hmaerki/experiment_octoprobe_testbed_heatguard/kicad/heatguard_v0.3/production_v0.3/pcb_top_3D.png

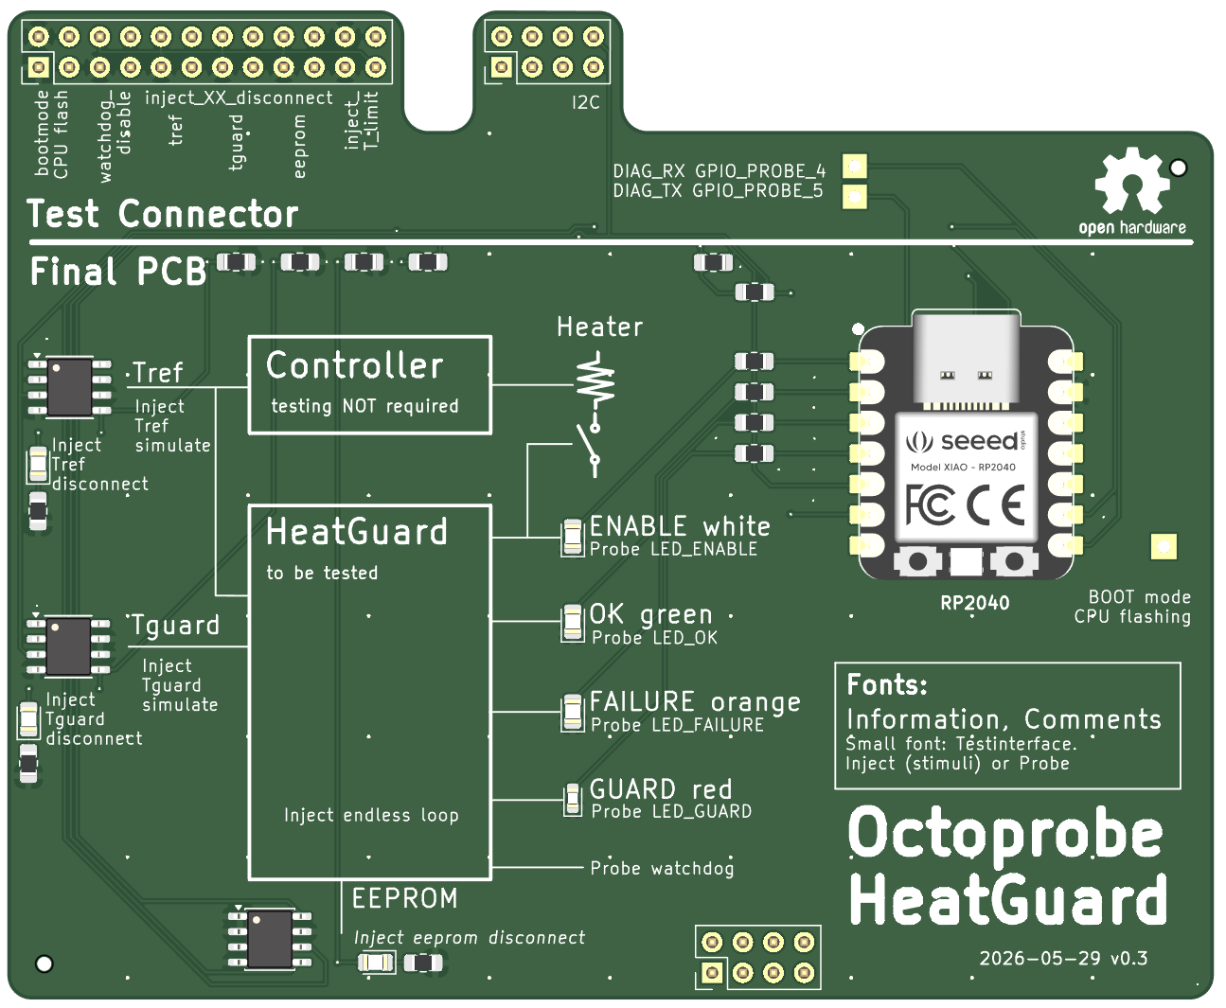
kicad/heatguard_v0.3/production_v0.3/pcb_top_3D.png
