hmaerki/experiment_octoprobe_testbed_heatguard/experiments/micropython_ds20_simulator/main.py

"""
DS18B20 1-Wire Slave Implementation for Raspberry Pi Pico

This file contains MicroPython code running on a Raspberry Pi Pico.

GPIO Configuration:
- GPIO2: Connected to a 1-Wire bus (open-drain with 4.7k pull-up)

This Pico acts as a 1-WIRE SLAVE and emulates two DS18B20 temperature sensors:
- Sensor 1: ROM 28 5A 3F 7B 05 00 00 0F → 18°C
- Sensor 2: ROM 28 5A 3F 7B 05 00 00 00 → 12°C

Reference: https://www.analog.com/media/en/technical-documentation/data-sheets/ds18b20.pdf

The implementation handles:
- 1-Wire reset and presence pulse detection
- ROM identification and matching (SEARCH_ROM, MATCH_ROM, SKIP_ROM)
- Temperature conversion requests
- Scratchpad memory read/write operations
"""

import time

import machine
from micropython import const

# ============================================================================
# GPIO Configuration
# ============================================================================

ONEWIRE_PIN = 2  # GPIO2 - 1-Wire data line
onewire_pin = machine.Pin(ONEWIRE_PIN, machine.Pin.OPEN_DRAIN, machine.Pin.PULL_UP)

# ============================================================================
# 1-Wire Timing Constants (microseconds)
# ============================================================================

RESET_LOW_TIME = const(480)  # Master reset pulse duration
PRESENCE_DELAY = const(30)  # Delay before responding with presence
PRESENCE_PULSE_TIME = const(60)  # Our presence pulse duration
READ_SAMPLE_TIME = const(15)  # Time to read bit during read slot
WRITE_0_TIME = const(60)  # Hold time for writing 0
WRITE_1_TIME = const(15)  # Hold time for writing 1
BIT_SLOT_TIME = const(60)  # Total time per bit slot

# ============================================================================
# 1-Wire Command Codes
# ============================================================================

CMD_SEARCH_ROM = const(0xF0)
CMD_READ_ROM = const(0x33)
CMD_MATCH_ROM = const(0x55)
CMD_SKIP_ROM = const(0xCC)
CMD_ALARM_SEARCH = const(0xEC)
CMD_CONVERT_TEMP = const(0x44)
CMD_WRITE_SCRATCHPAD = const(0x4E)
CMD_READ_SCRATCHPAD = const(0xBE)
CMD_COPY_SCRATCHPAD = const(0x48)
CMD_RECALL_E2 = const(0xB8)
CMD_READ_POWER_SUPPLY = const(0xB4)

# ============================================================================
# Sensor Configuration
# ============================================================================

FAMILY_CODE = const(0x28)  # DS18B20 family code

# Define two virtual sensors with their ROM codes and temperatures
SENSORS = [
    {
        "rom": bytes([0x28, 0x5A, 0x3F, 0x7B, 0x05, 0x00, 0x00, 0x0F]),
        "temp": 18.0,
        "name": "Sensor 1",
    },
    {
        "rom": bytes([0x28, 0x5A, 0x3F, 0x7B, 0x05, 0x00, 0x00, 0x00]),
        "temp": 12.0,
        "name": "Sensor 2",
    },
]

# ============================================================================
# CRC-8 Calculation
# ============================================================================


def crc8(data):
    """Calculate CRC-8 for 1-Wire (polynomial 0x31)"""
    crc = 0
    for byte in data:
        crc ^= byte
        for _ in range(8):
            if crc & 0x01:
                crc = (crc >> 1) ^ 0x8C
            else:
                crc >>= 1
    return crc & 0xFF


# ============================================================================
# Scratchpad Memory Class
# ============================================================================


class Scratchpad:
    """DS18B20 Scratchpad memory (9 bytes)"""

    def __init__(self, temp=20.0):
        self.set_temperature(temp)
        self.th = 0x4B  # Byte 2: TH (75°C)
        self.tl = 0x46  # Byte 3: TL (70°C)
        self.config = 0x7F  # Byte 4: CONFIG (12-bit resolution)

    def set_temperature(self, celsius):
        """Set temperature in Celsius and encode to LSB/MSB"""
        # Clamp temperature to valid range
        celsius = max(-55.0, min(125.0, celsius))

        # Convert to 1/16°C units
        temp_int = int(celsius * 16)

        # Encode as 16-bit signed
        if temp_int < 0:
            temp_int = (((-temp_int) ^ 0xFFFF) + 1) & 0xFFFF

        self.temp_lsb = temp_int & 0xFF
        self.temp_msb = (temp_int >> 8) & 0xFF

    def to_bytes(self):
        """Convert scratchpad to 9-byte array"""
        data = bytes(
            [
                self.temp_lsb,
                self.temp_msb,
                self.th,
                self.tl,
                self.config,
                0xFF,  # Reserved
                0x00,  # Reserved
                0x00,  # Reserved
                0x00,  # CRC (will be filled)
            ]
        )

        # Calculate CRC for bytes 0-7
        crc = crc8(data[0:8])
        data = data[0:8] + bytes([crc])

        return data


# ============================================================================
# 1-Wire Slave Implementation
# ============================================================================


class OneWireSlave:
    """1-Wire Slave implementation for DS18B20 emulation"""

    def __init__(self, pin, sensors):
        self.pin = pin
        self.sensors = sensors
        self.selected_sensor = None
        self.rom_bit_index = 0
        self.conversion_active = False

    def wait_for_reset(self):
        """Wait for a 1-Wire reset pulse from master"""
        # Wait for line to go low (reset pulse from master)
        timeout = 1000  # 1 second timeout
        count = 0

        while self.pin.value() and count < timeout:
            time.sleep_us(100)
            count += 1

        if count >= timeout:
            return False

        # Wait for reset pulse to complete (480-960 us)
        time.sleep_us(RESET_LOW_TIME)

        # Check if line is still low (valid reset pulse)
        if not self.pin.value():
            return False

        # Send presence pulse
        self.send_presence_pulse()
        return True

    def send_presence_pulse(self):
        """Send presence pulse to indicate we're on the bus"""
        # Wait a bit before pulling line low
        time.sleep_us(PRESENCE_DELAY)

        # Pull line low for presence pulse
        self.pin.value(0)
        time.sleep_us(PRESENCE_PULSE_TIME)

        # Release line
        self.pin.value(1)

    def read_bit(self):
        """Read a bit from the 1-Wire bus"""
        # Wait for master to pull line low
        timeout = 100
        count = 0
        while self.pin.value() and count < timeout:
            time.sleep_us(1)
            count += 1

        if count >= timeout:
            return None

        # Wait for proper read sample time
        time.sleep_us(READ_SAMPLE_TIME)

        # Sample the bit (1 = line is high, 0 = line is low)
        bit = self.pin.value()

        # Wait for rest of bit slot
        time.sleep_us(BIT_SLOT_TIME - READ_SAMPLE_TIME)

        return bit

    def write_bit(self, bit):
        """Write a bit to the 1-Wire bus"""
        if bit:
            # Write 1: let line float high (very brief pull-down or none)
            self.pin.value(1)
            time.sleep_us(WRITE_1_TIME)
        else:
            # Write 0: pull line low
            self.pin.value(0)
            time.sleep_us(WRITE_0_TIME)
            self.pin.value(1)

        # Wait for rest of bit slot
        time.sleep_us(BIT_SLOT_TIME - (WRITE_1_TIME if bit else WRITE_0_TIME))

    def read_byte(self):
        """Read a byte from the 1-Wire bus (LSB first)"""
        byte = 0
        for i in range(8):
            bit = self.read_bit()
            if bit is None:
                return None
            if bit:
                byte |= 1 << i
        return byte

    def write_byte(self, byte):
        """Write a byte to the 1-Wire bus (LSB first)"""
        for i in range(8):
            bit = (byte >> i) & 1
            self.write_bit(bit)

    def handle_search_rom(self):
        """Handle ROM SEARCH command"""
        # Send ROM bits with collision detection
        # For simplicity in slave mode, we'll handle single device addressing
        pass

    def handle_skip_rom(self):
        """Handle SKIP ROM command - select all devices"""
        self.selected_sensor = self.sensors[0] if len(self.sensors) == 1 else None

    def handle_match_rom(self):
        """Handle MATCH ROM command - select device by ROM code"""
        rom = bytes(self.read_byte() for _ in range(8))

        # Find matching sensor
        for sensor in self.sensors:
            if sensor["rom"] == rom:
                self.selected_sensor = sensor
                return True

        return False

    def handle_convert_temp(self):
        """Handle CONVERT TEMPERATURE command"""
        self.conversion_active = True
        # Simulate conversion delay (750ms for 12-bit)
        time.sleep_ms(750)
        self.conversion_active = False

    def handle_read_scratchpad(self):
        """Handle READ SCRATCHPAD command"""
        if not self.selected_sensor:
            return

        # Create scratchpad with current temperature
        scratchpad = Scratchpad(self.selected_sensor["temp"])
        data = scratchpad.to_bytes()

        # Send all 9 bytes
        for byte in data:
            self.write_byte(byte)

    def handle_write_scratchpad(self):
        """Handle WRITE SCRATCHPAD command"""
        if not self.selected_sensor:
            return

        # Read TH, TL, CONFIG
        th = self.read_byte()
        tl = self.read_byte()
        config = self.read_byte()

        if th is None or tl is None or config is None:
            return

        # Update scratchpad (in real device, would update EEPROM later)
        scratchpad = Scratchpad(self.selected_sensor["temp"])
        scratchpad.th = th
        scratchpad.tl = tl
        scratchpad.config = config

    def run(self):
        """Main 1-Wire slave loop"""
        print("DS18B20 1-Wire Slave Starting...")
        print(f"GPIO{ONEWIRE_PIN}: 1-Wire Bus Monitor")
        print("Available sensors:")
        for sensor in SENSORS:
            rom_str = "".join(f"{b:02X} " for b in sensor["rom"])
            print(f"  {sensor['name']}: {rom_str} → {sensor['temp']}°C")
        print("\nWaiting for 1-Wire commands...\n")

        while True:
            try:
                # Wait for master to initiate communication with reset pulse
                if not self.wait_for_reset():
                    continue

                print("[RESET] Presence pulse sent")

                # Read command byte
                cmd = self.read_byte()
                if cmd is None:
                    continue

                print(f"Command: 0x{cmd:02X}")

                # Handle command
                if cmd == CMD_SEARCH_ROM:
                    print("  → SEARCH ROM")
                    # Not fully implemented for simplicity

                elif cmd == CMD_READ_ROM:
                    print("  → READ ROM")
                    if len(self.sensors) == 1:
                        self.selected_sensor = self.sensors[0]
                        rom = self.selected_sensor["rom"]
                        print(f"    Sending ROM: {rom.hex()}")
                        for byte in rom:
                            self.write_byte(byte)

                elif cmd == CMD_MATCH_ROM:
                    print("  → MATCH ROM")
                    if self.handle_match_rom():
                        rom_str = "".join(
                            f"{b:02X}" for b in self.selected_sensor["rom"]
                        )
                        print(f"    Matched: {rom_str}")

                elif cmd == CMD_SKIP_ROM:
                    print("  → SKIP ROM")
                    if len(self.sensors) == 1:
                        self.selected_sensor = self.sensors[0]

                elif cmd == CMD_CONVERT_TEMP:
                    print("  → CONVERT TEMPERATURE")
                    self.handle_convert_temp()
                    print("    Conversion complete")

                elif cmd == CMD_READ_SCRATCHPAD:
                    print("  → READ SCRATCHPAD")
                    self.handle_read_scratchpad()
                    print("    Scratchpad sent")

                elif cmd == CMD_WRITE_SCRATCHPAD:
                    print("  → WRITE SCRATCHPAD")
                    self.handle_write_scratchpad()
                    print("    Scratchpad updated")

                elif cmd == CMD_READ_POWER_SUPPLY:
                    print("  → READ POWER SUPPLY")
                    self.write_byte(1)  # External power
                    print("    Power: External")

                else:
                    print("  → Unknown command")

            except Exception as e:
                print(f"Error: {e}")
                time.sleep_ms(100)


# ============================================================================
# Main
# ============================================================================

if __name__ == "__main__":
    slave = OneWireSlave(onewire_pin, SENSORS)
    slave.run()
